ctranstrum/lintilla/images/allitnil-lintilla.png

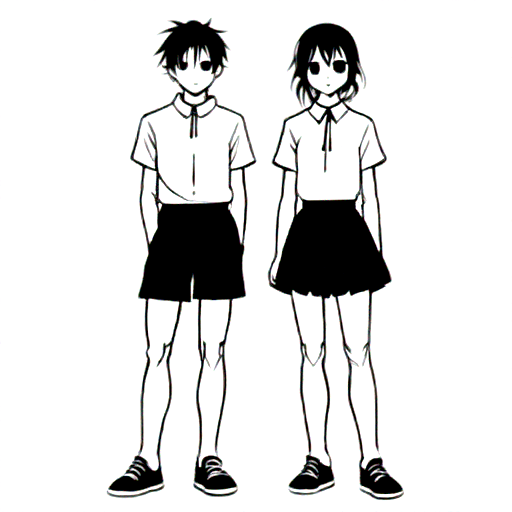
images/allitnil-lintilla.png
