ctranstrum/lintilla/images/pcb-allitnil.jpg

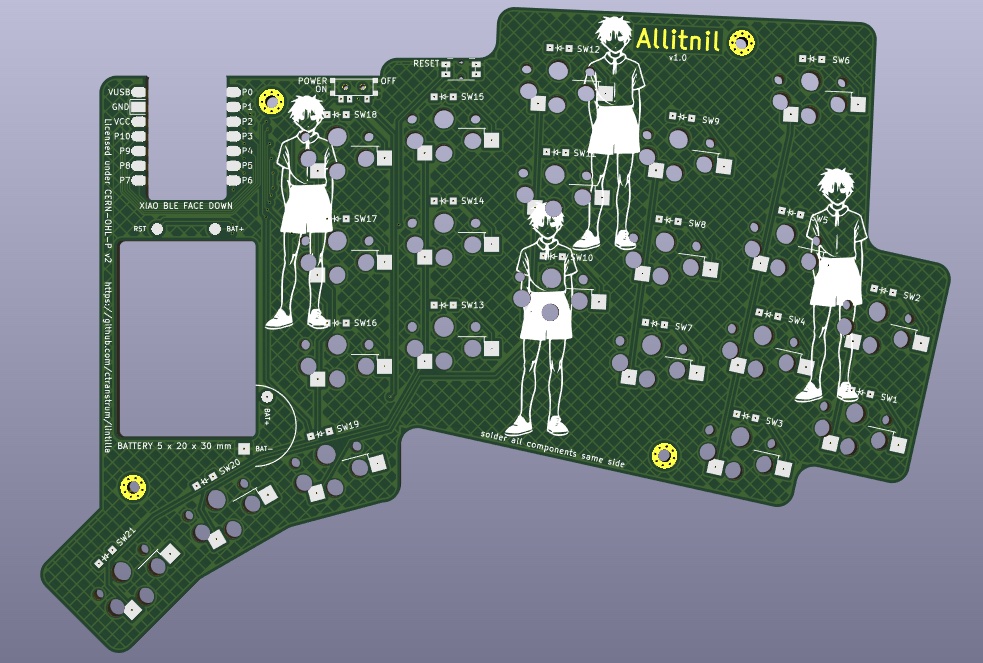
images/pcb-allitnil.jpg
