ctranstrum/lintilla/images/pcb-lintilla.jpg

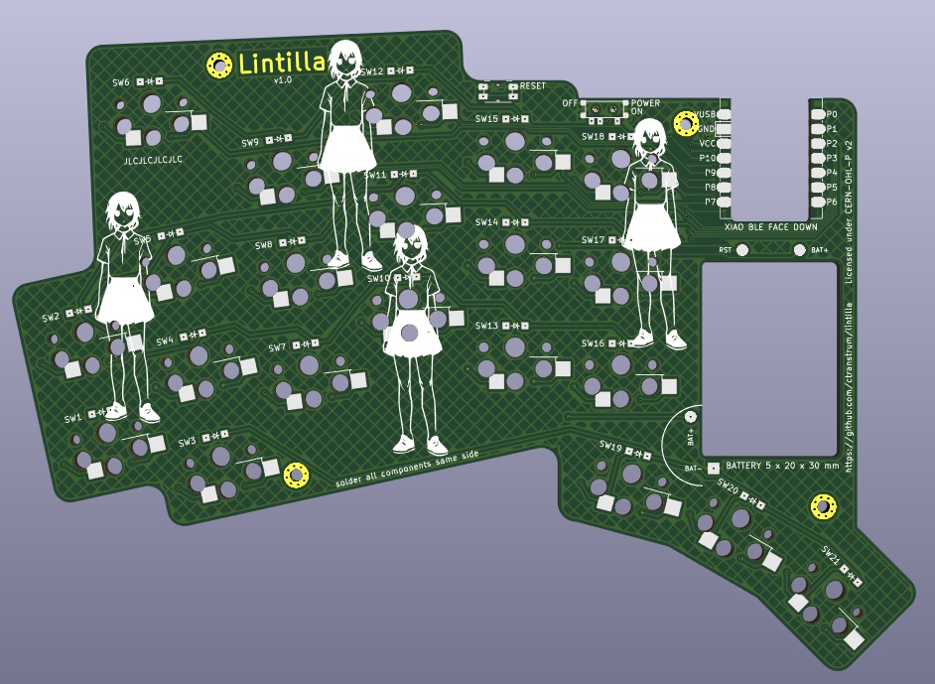
images/pcb-lintilla.jpg
